adaand00/heptachron/CAD/Pre/Heptachron_window.dxf

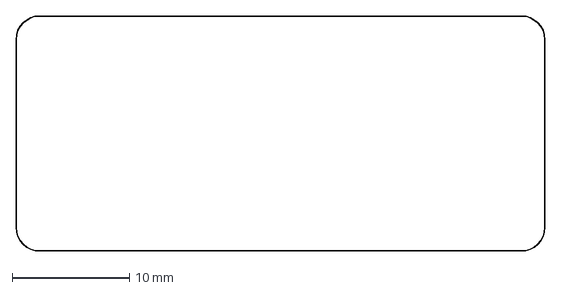
[picture p20: CAD file, 2024-04-20]
CAD/Pre/Heptachron_window.dxf
45.0 x 20.0 mm
