adaand00/heptachron/CAD/v2/Hepta_spacer v4.stl

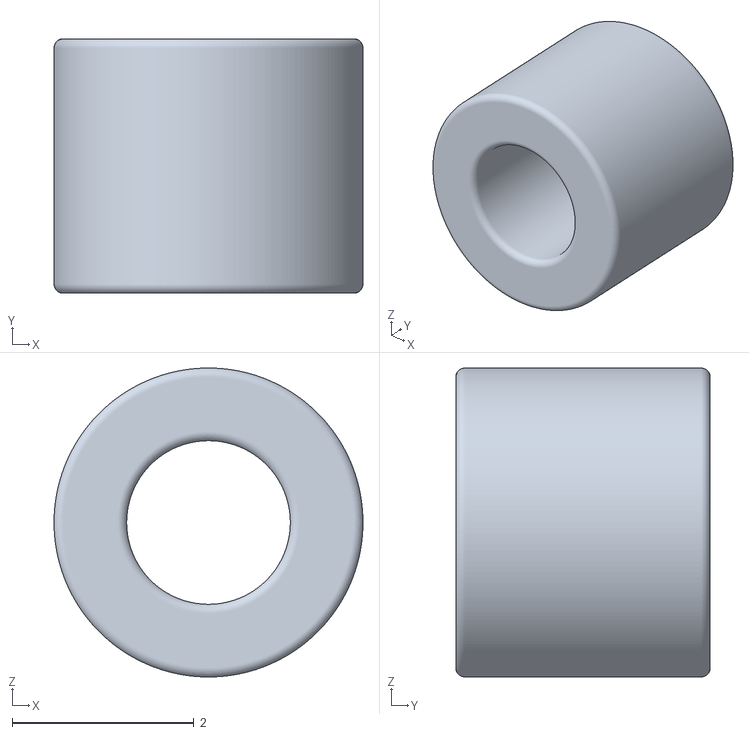
[picture p21: CAD file, 2024-11-16]
CAD/v2/Hepta_spacer v4.stl
3.40 x 2.80 x 3.40
