adaand00/heptachron/CAD/Pre/Male heptachronnector.stl

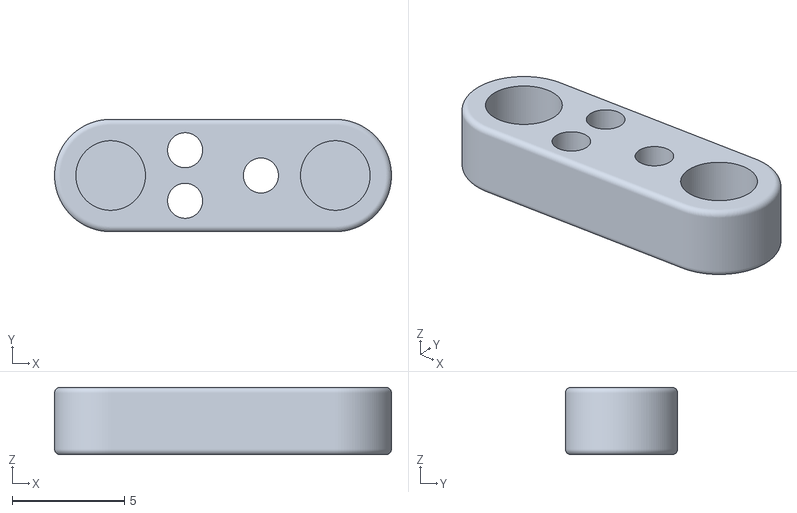
[picture p22: CAD file, 2024-04-20]
CAD/Pre/Male heptachronnector.stl
15.0 x 5.00 x 3.00
