adaand00/heptachron/CAD/v2/Button_base.stl

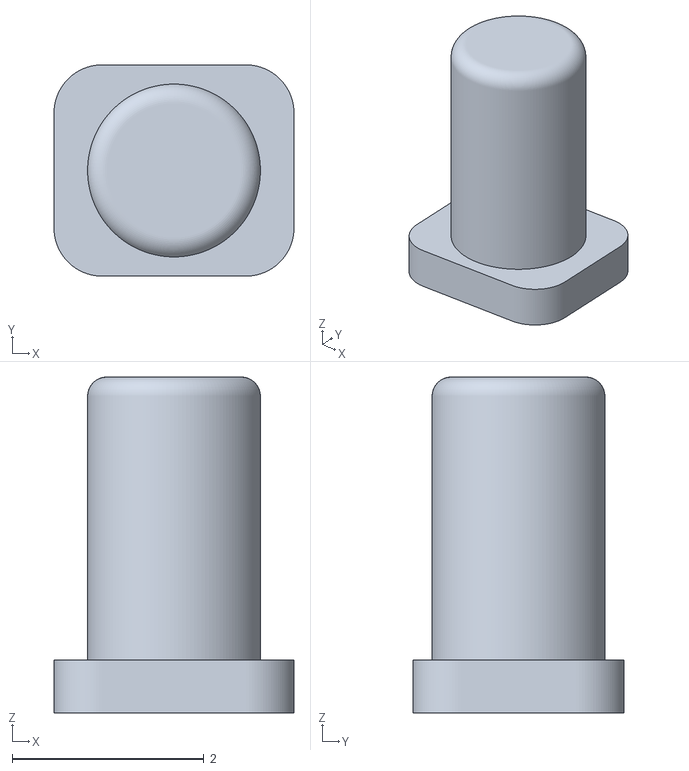
[picture p23: CAD file, 2024-11-16]
CAD/v2/Button_base.stl
2.50 x 2.20 x 3.50
